diyruz/geiger/Source/preinclude.h

#define TC_LINKKEY_JOIN
#define NV_INIT
#define NV_RESTORE

#define TP2_LEGACY_ZC
// patch sdk
// #define ZDSECMGR_TC_ATTEMPT_DEFAULT_KEY TRUE

#define NWK_AUTO_POLL
#define MULTICAST_ENABLED FALSE

#define ZCL_READ
#define ZCL_WRITE
#define ZCL_BASIC
#define ZCL_IDENTIFY
#define ZCL_REPORTING_DEVICE
#define ZCL_ON_OFF

#define DISABLE_GREENPOWER_BASIC_PROXY
#define BDB_FINDING_BINDING_CAPABILITY_ENABLED 1
#define BDB_REPORTING TRUE

#ifdef DEFAULT_CHANLIST
#undef DEFAULT_CHANLIST
#endif
#define DEFAULT_CHANLIST 0x07FFF800

#define HAL_BUZZER FALSE
#define HAL_KEY FALSE

#define HAL_LED TRUE
#define HAL_ADC FALSE
#define HAL_LCD FALSE

#define BLINK_LEDS TRUE

// one of this boards
// #define HAL_BOARD_TARGET
// #define HAL_BOARD_CHDTECH_DEV

#if !defined(HAL_BOARD_TARGET) && !defined(HAL_BOARD_CHDTECH_DEV)
#error "Board type must be defined"
#endif

#if defined(HAL_BOARD_TARGET)
#define APP_TX_POWER TX_PWR_PLUS_19
#elif defined(HAL_BOARD_CHDTECH_DEV)
#define APP_TX_POWER TX_PWR_PLUS_4
#define DO_DEBUG_UART
// #define DO_DEBUG_MT
#endif



#ifdef DO_DEBUG_UART
#define HAL_UART TRUE
#define HAL_UART_DMA 1
#define INT_HEAP_LEN (2685 - 0x4B - 0xBB)
#endif

#ifdef DO_DEBUG_MT
#define HAL_UART TRUE
#define HAL_UART_DMA 1
#define HAL_UART_ISR 2
#define INT_HEAP_LEN (2685 - 0x4B - 0xBB)

#define MT_TASK

#define MT_UTIL_FUNC
#define MT_UART_DEFAULT_BAUDRATE HAL_UART_BR_115200
#define MT_UART_DEFAULT_OVERFLOW FALSE

#define ZTOOL_P1

#define MT_APP_FUNC
#define MT_APP_CNF_FUNC
#define MT_SYS_FUNC
#define MT_ZDO_FUNC
#define MT_ZDO_MGMT
#define MT_DEBUG_FUNC

#endif


#include "hal_board_cfg.h"
